NemoAndrea/SpotiStation/src/bootmenu.py

import socket
import time
import math
from config_manager import get_playlists_in_config_as_sorted_list, write_playlist_config, get_device_config, write_device_config
import configparser
import logging


''''Boot mode selection

To keep the ui simple, there are few buttons on the device. To avoid complex multi-button 
commands, the device will wait a few seconds when starting the player in this 'boot menu'
which allows for a few utility menus/selection panels. Of course the easiest is to ssh into the
device, but for quick on the go or for less tech savy users these menus can be useful.
'''

def query_boot_mode(player, duration=5):
    '''Main loop that allows for boot mode selection'''
    logger = logging.getLogger()
    logger.info(f">> Waiting for boot mode selection - limit={duration} sec")
    initial_time = time.time()  
    seconds_since_start = -1
    
    # wait for button press until 'duration' has passed. If loop expires, then None is returned
    while time.time()-initial_time < duration:
        if any([player.playpause.got_pressed(), player.sidebutton_1.got_pressed(),player.sidebutton_2.got_pressed()]):
            logger.info("> Skipped boot menu")
            break
        elif any((player.backbutton_1.got_pressed(), player.backbutton_2.got_pressed())):
            logger.info("> Launching Configuration Menu")
            display_config_menu(player); break 
        # update the text on display once per second
        if seconds_since_start != math.floor(time.time()-initial_time):
            seconds_since_start = math.floor(time.time()-initial_time)
            player.display.add_text_to_overlay("Press button", (32, 52),
             fill=(255,255,255,200), clear=True)  
            player.display.add_text_to_overlay(f"for config {duration-seconds_since_start}", (32, 60),
             fill=(255,255,255,200), clear=False)  
            player.display.add_overlay_to_display(dimming=0.5)
        time.sleep(0.01)

    logger.info("> Leaving Boot Menu, launching application as normal")
    player.display.add_text_to_overlay(f"starting...", (32, 60), fill=(255,255,255,200), clear=True)  
    player.display.add_overlay_to_display(dimming=0.7)
    time.sleep(0.5)
    return None  # if we wait the full duration


def display_config_menu(player, duration=30):
    '''Configuration/boot menu that allows setting a few player options without ssh
    
    The menu will automatically exit if no action is chosen within 30 seconds. This is in case
    someone accidentally opened the menu and is not sure what to do.'''
    initial_time = time.time()  
    current_item_index = 0  # current item in list that is selected
    options = ["-- exit --", "manual", "playlists", "ip adress", "bluetooth"] 
    
    # wait for button press until 'duration' has passed. If loop expires, then None is returned
    while time.time()-initial_time < duration:
        player.display.add_text_to_overlay("Config Menu", (32, 5), fill=(0,139,139,255), clear=True)        

        # display the options on screen
        for i, option in enumerate(options):
            if current_item_index == i:
                color = (248,221,116,255)  # make text yellow
                textfill = "> "  # add '> {optiontext}' to further clarify that this option is selected
            else:
                color = (255,255,255,180)
                textfill = ""  # no leading text
            player.display.add_text_to_overlay(f"{textfill}{option}", (10, 14+i*6),
             fill=color, clear=False, center=False) 

        # actually show the overlay
        player.display.add_overlay_to_display(dimming=0.9)  

        # the playpause button serves as the 'select' key, so when that is pressed we choose that option 
        if player.playpause.got_pressed(): 
            if current_item_index == 0: return  # exit menu, just return without doing anything
            elif current_item_index == 1: show_manual_qr_code(player); return
            elif current_item_index == 2: select_playlists_on_display(player); return
            elif current_item_index == 3: display_ip_info(player); return
            elif current_item_index == 4: toggle_bluetooth_skip_state(player); return
            # add more options here
        
        if player.sidebutton_2.got_pressed():
            if current_item_index > 0:  # check we cannot exceed the list of options
                current_item_index -= 1
        elif player.sidebutton_1.got_pressed():
            if current_item_index < (len(options)-1):  # check we cannot exceed the list of options
                current_item_index += 1       


        time.sleep(0.02)
    return

def show_manual_qr_code(player):
    '''Show a scannable QR code linking to the project wiki (i.e. device manual)'''

    logger = logging.getLogger()
    logger.info("Showing SpotiPlayer manual QR code")

    player.display.set_image_from_file("./media/interface/manual_qr.png")
    player.display.add_text_to_overlay("scan QR code", (32, 6), fill=(255,255,255,200), clear=True)
    player.display.add_text_to_overlay("for manual", (32, 57), fill=(255,255,255,200), clear=False)    
    player.display.add_overlay_to_display(dimming=0) 

    # wait until ok button is pressed
    while not player.playpause.got_pressed():
        time.sleep(0.03)

    return  # leave the menu and boot


def display_ip_info(player):
    '''Display the local IP adress on screen for SSH connection
    
    Show the local IP adress on screen. In case you need to connect to the device via SSH but do
    not use a fixed IP adress. Playpause button will exit the menu and start the player.'''

    logger = logging.getLogger()
    logger.info("Showing SpotiPlayer IP address")

    s = socket.socket(socket.AF_INET, socket.SOCK_DGRAM)
    s.connect(("8.8.8.8", 80))
    
    logger.info(f"IP Address of {socket.gethostname()}: {s.getsockname()[0]}")
    player.display.set_image_from_file("./media/interface/ip_screen.png")
    player.display.add_text_to_overlay(str(s.getsockname()[0]), (32, 50),
     fill=(255,255,255,200), clear=True)  
    player.display.add_overlay_to_display(dimming=0)  

    # wait until ok button is pressed
    while not player.playpause.got_pressed():
        time.sleep(0.03)

    return  # leave the menu and boot


def select_playlists_on_display(player):
    '''Display the user's spotify playlists, their status and change the status
    
    Shows all the playlists associated with the spotify account. Green playlists are 'in rotation',
    while 'gray' playlists are ignored. Use side buttons for up-down navigation and playpause button
    to toggle the state of the playlist. Use the 'save' option (top of the list) to save config and
    start the player.'''

    logger = logging.getLogger()
    logger.info("Configuring playlist states...")

    display_limit = 8  # how many items for on one screen
    playlists = get_playlists_in_config_as_sorted_list()
    playlists.insert(0, ["-- save --", False])
    caroussel_offset = 0  # keep track of which playlists fit on the screen
    cursor_position = 0
    while True:        
        # show page header
        player.display.add_text_to_overlay("playlist state", (32, 5), fill=(0,139,139,255), clear=True)

        # show playlists
        for i, (playlist, in_rotation) in enumerate(playlists):
            if caroussel_offset <= i < caroussel_offset+display_limit:  
                # do nothing if i=0 and caroussel>0, as then i=0 location is occupied by 'more'                  
                if not (caroussel_offset > 0 and i-caroussel_offset==0):                    
                    color = (0, 255, 0, 255) if in_rotation else (255,255, 255, 80)
                    if i==cursor_position:
                        filltext = "> "
                        text_x = 0
                    else:
                        filltext = ""
                        text_x = 5
                    player.display.add_text_to_overlay(f"{filltext}{playlist}", (text_x, 12 +
                     (i-caroussel_offset)*6), fill=color, clear=False, center=False)

        # display '...MORE' if more content can be revelead by scroll (moving cursor)
        if display_limit+caroussel_offset-1 < len(playlist):
            player.display.add_text_to_overlay("...more", (5, 60), fill=(248,221,116,255),
             clear=False, center=False)
        if caroussel_offset > 0:
            player.display.add_text_to_overlay("...more", (5, 12), fill=(248,221,116,255),
             clear=False, center=False)     
        
        # actually show the overlay
        player.display.add_overlay_to_display(dimming=0.9)     

        if player.sidebutton_2.got_pressed():
            if cursor_position > 0:  # check we cannot exceed the list of options
                cursor_position -= 1
            if cursor_position-1 < caroussel_offset:
                if caroussel_offset != 0: caroussel_offset -=1
        elif player.sidebutton_1.got_pressed():
            if cursor_position < (len(playlists)-1):  # check we cannot exceed the list of options
                cursor_position += 1  
            if cursor_position+1 > caroussel_offset+display_limit:
                caroussel_offset +=1

                
        if player.playpause.got_pressed():
            if cursor_position == 0:  # save and exit option
                logger.info("Saving playlist state config.")
                # get the old config
                config = configparser.ConfigParser(allow_no_value=True)
                config.read("config/playlists.ini")
                # get the new user selection
                in_rotation = list(filter(lambda x: x[1], playlists[1:]))
                ignored = list(filter(lambda x: not x[1], playlists[1:]))

                for new_playlist, _ in in_rotation:
                    if new_playlist not in [key for key in config["in rotation"]]:
                        # swap to in_rotation
                        logger.info(f"[config change] (new in-rotation): {new_playlist}")
                        # we get the uri from the old section (which is the 'ignored' section)
                        uri = config.get("ignored", new_playlist)
                        config.remove_option("ignored", new_playlist)
                        config.set("in rotation", new_playlist, uri)
                for new_playlist, _ in ignored:
                    if new_playlist not in [key for key in config["ignored"]]:
                        # swap to ignored
                        logger.info(f"[config change] (new ignored): {new_playlist}")
                        # we get the uri from the old section (which is the 'in rotation' section)
                        uri = config.get("in rotation", new_playlist)
                        config.remove_option("in rotation", new_playlist)
                        config.set("ignored", new_playlist, uri)
                
                write_playlist_config(config)
                return
            else:  
                # we are toggling the state of the playlist 'ignored'<->'in rotation'
                logger.debug(f"changing the state of {playlists[cursor_position][0]} to {not playlists[cursor_position][1]} (unsaved)")
                playlists[cursor_position][1] = not playlists[cursor_position][1]
        
        time.sleep(0.02)


def toggle_bluetooth_skip_state(player):
    '''Toggle the state of the bluetooth skip state and update in config. 
    can be used for situations where you are developing for the system without a bluetooth device
    nearby, or if you are using a usb-to-audio adapter card and a wired audio connection'''

    logger = logging.getLogger()
    logger.info("Toggling bluetooth state")

    config = get_device_config()  # get whatever was configured before
    new_bluetooth_state = not config.getboolean('connectivity', 'skip-bluetooth')
    logger.info(f"Switching skip-bluetooth (player.ini) from {not new_bluetooth_state} to {new_bluetooth_state}")

    player.display.add_text_to_overlay("Skip Bluetooth", (32, 5), fill=(0,139,139,255), clear=True)
    player.display.add_text_to_overlay("set to: " + str(new_bluetooth_state), (32, 50), fill=(0,139,139,255), clear=False)
    player.display.add_overlay_to_display(dimming=0.9)     

    if new_bluetooth_state:
        config['connectivity']['skip-bluetooth'] = "yes"
    else:
        config['connectivity']['skip-bluetooth'] = "no"

    write_device_config(config)
    logger.info(f"Wrote new skip-bluetooth (player.ini) value")

    time.sleep(0.5)

    # wait until ok button is pressed
    while not player.playpause.got_pressed():
        time.sleep(0.03)

    return
