NemoAndrea/SpotiStation/src/quiet_mode.py

from datetime import datetime
from setup_hardware import PlayerState
import logging

def quiet_mode_active(config):
    if config.getboolean('settings', 'night-mode-enabled'):
        current_time = datetime.now()
        # parse the config times. This will give objects with year = 1900
        starttime_raw = datetime.strptime(config['settings']['night-mode-time-start'], "%H:%M")
        endtime_raw = datetime.strptime(config['settings']['night-mode-time-end'], "%H:%M")
        # this is very clunky but it works and is not called frequently so it doesn't really matter
        starttime = datetime.now().replace(hour = starttime_raw.hour, minute = starttime_raw.minute)
        endtime = datetime.now().replace(hour = endtime_raw.hour, minute = endtime_raw.minute)
        #print(f"endtime {endtime} and starttime {starttime} and current {current_time}")
        if  current_time < endtime or current_time > starttime:       
            return True   # return True to inform that we should in QUIET mode
    else: 
        return False  # return False to inform that we can stay in current mode (ACTIVE or LOCKED)

def quiet_mode_enabled_since(config, time_since=30): 
    '''Check if a certain amount of time in minutes has expired since the start of QUIET mode'''
    current_time = datetime.now()
    # parse the config times. This will give objects with year = 1900
    starttime_raw = datetime.strptime(config['settings']['night-mode-time-start'], "%H:%M")
    endtime_raw = datetime.strptime(config['settings']['night-mode-time-end'], "%H:%M")
    endtime = datetime.now().replace(hour = endtime_raw.hour, minute = endtime_raw.minute)
    offset_minutes = time_since % 60
    offset_hours = time_since // 60
    offset_time = datetime.now().replace(
        hour = (starttime_raw.hour + offset_hours + (starttime_raw.minute + offset_minutes)//60) % 24,
        minute = (starttime_raw.minute + offset_minutes) % 60
    )

    # check if time_since minutes have passed since QUIET mode started
    # or if current time is before the end time (e.g 01:20 < 9:00)
    # TODO make this more robust (drop assumption that start time is <23:59 and end time in morning)
    if current_time > offset_time or current_time < endtime:       
        return False   # we have in in quiet mode for time_since minutes or more
    else:
        return False


def enable_quiet_mode(player, spotipy, config):
    logging.getLogger().info("Entering QUIET mode; pausing music and turning volume to 0")
    spotipy.pause_playback()  # pause the music via API (but could be turned back on via phone)
    set_display_quiet_mode(player, config)
    player.state = PlayerState.QUIET


def set_display_quiet_mode(player, config):
    player.display.set_display_mode("quiet_mode") 
    player.display.add_text_to_overlay(f"Wake at {config['settings']['night-mode-time-end']}",
     (32, 60), fill=(255,255,255,200))  
    player.display.add_overlay_to_display(dimming=0.95)


def enable_locked_mode(player, spotipy, config):
    logging.getLogger().info("Entering LOCKED mode; pausing music and turning volume to 0 until the next QUIET mode")
    spotipy.pause_playback()  # pause the music via API (but could be turned back on via phone)
    player.display.set_display_mode("lock_mode") 
    player.display.add_text_to_overlay(f"until {config['settings']['night-mode-time-start']}",
     (32, 58), fill=(255,255,255,200))  
    player.display.add_overlay_to_display(dimming=0.95)
    player.state = PlayerState.LOCKED
